ericwooshem/DIY-Frugal-Arduino-CO2-Sensor/Graphics/CO2_Sensor_Complete.png

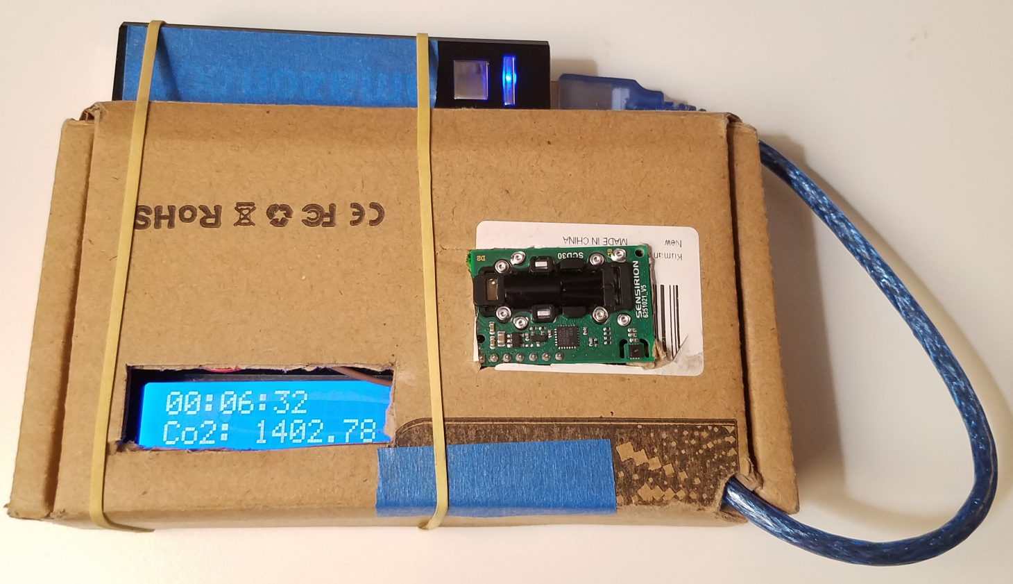
Graphics/CO2_Sensor_Complete.png
