ericwooshem/DIY-Frugal-Arduino-CO2-Sensor/Graphics/CO2_Sensor_Insides.png

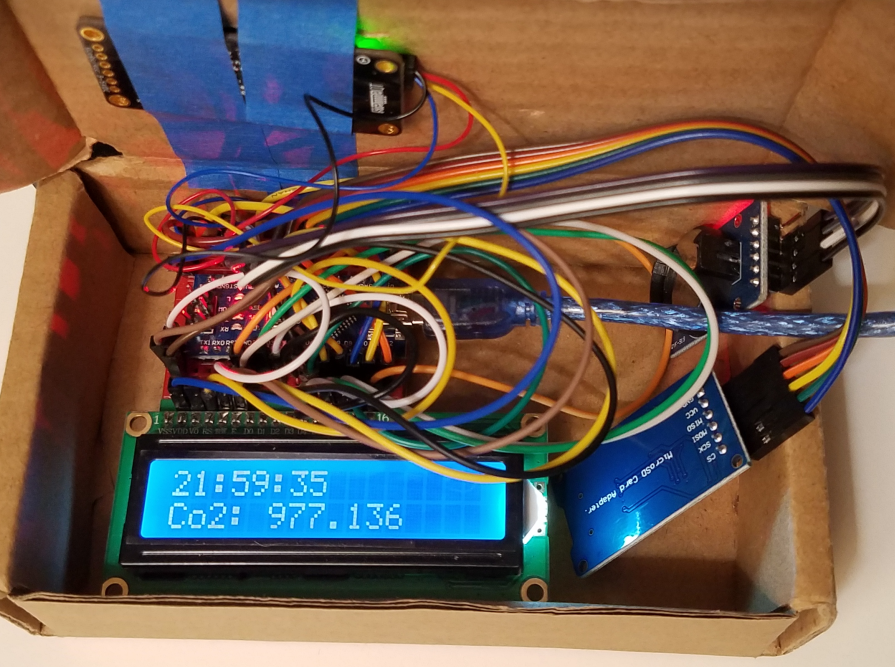
Graphics/CO2_Sensor_Insides.png
