ericwooshem/DIY-Frugal-Arduino-CO2-Sensor/Graphics/FileImporting/CO2_Excel_TextImportMethod.png

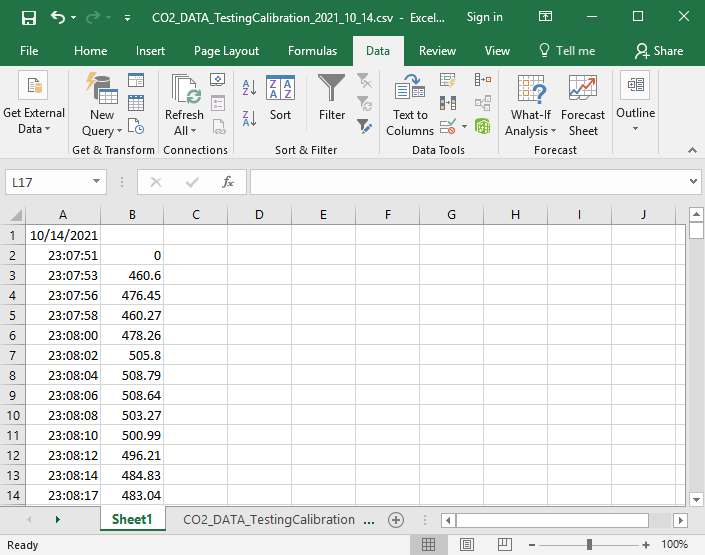
Graphics/FileImporting/CO2_Excel_TextImportMethod.png
