ericwooshem/DIY-Frugal-Arduino-CO2-Sensor/Graphics/FileImporting/CO2_Excel_UhOh.png

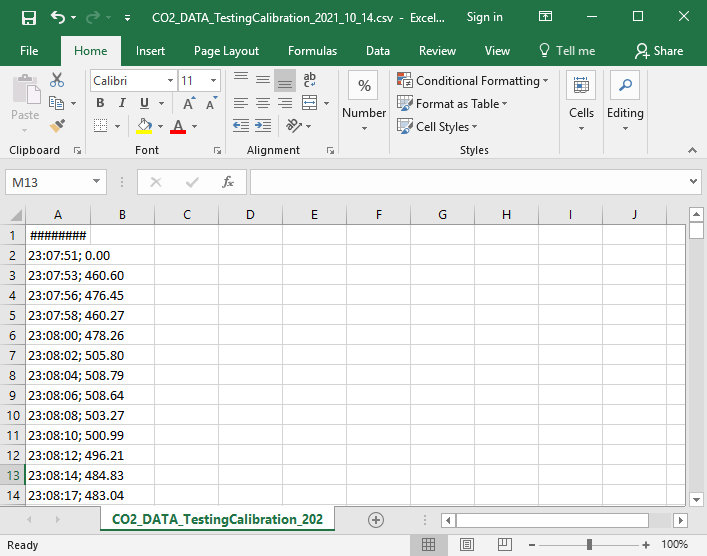
Graphics/FileImporting/CO2_Excel_UhOh.png
