ericwooshem/DIY-Frugal-Arduino-CO2-Sensor/Graphics/I12.png

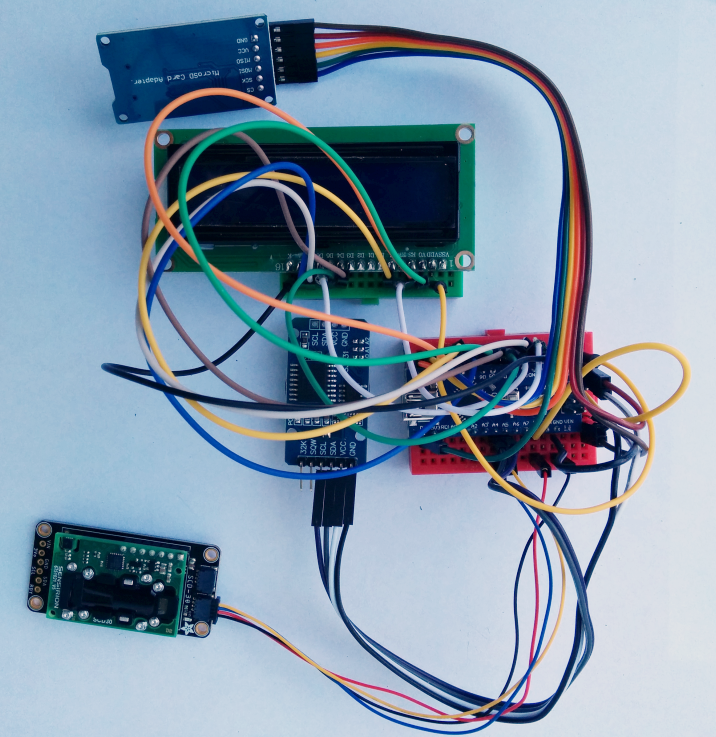
Graphics/I12.png
