ericwooshem/DIY-Frugal-Arduino-CO2-Sensor/Graphics/I13.png

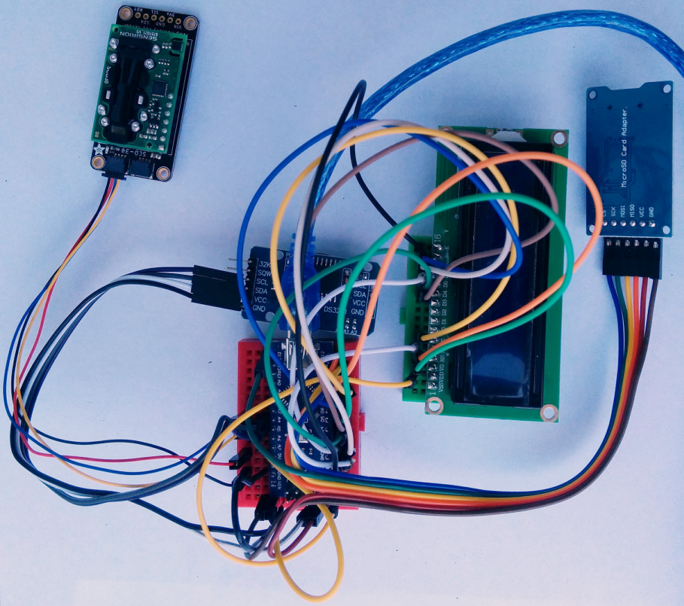
Graphics/I13.png
