ericwooshem/DIY-Frugal-Arduino-CO2-Sensor/Graphics/I14.png

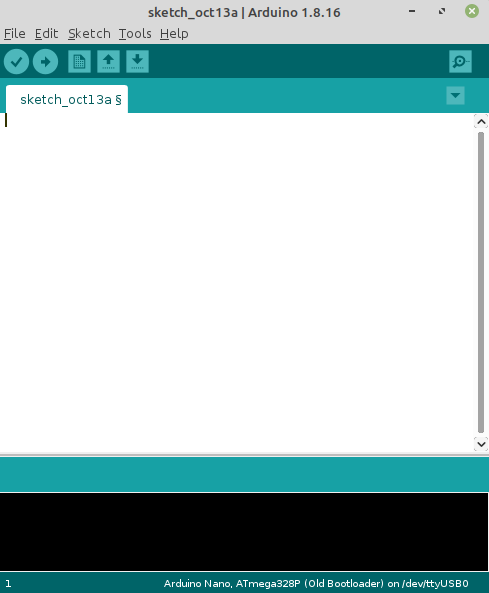
Graphics/I14.png
