ericwooshem/DIY-Frugal-Arduino-CO2-Sensor/Graphics/I17.png

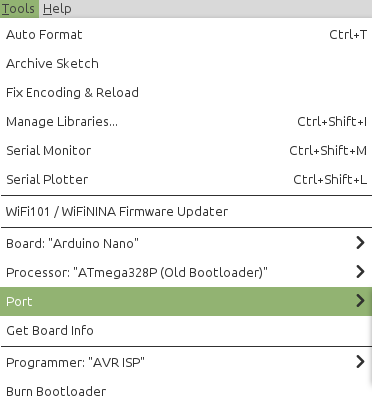
Graphics/I17.png
