ericwooshem/DIY-Frugal-Arduino-CO2-Sensor/Graphics/I19.png

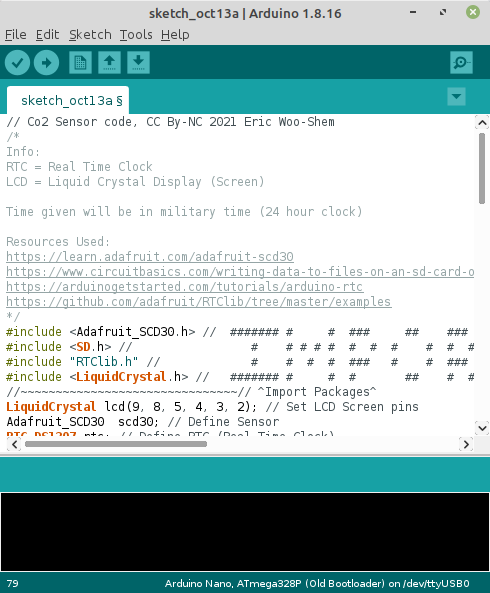
Graphics/I19.png
