ericwooshem/DIY-Frugal-Arduino-CO2-Sensor/Graphics/I20.png

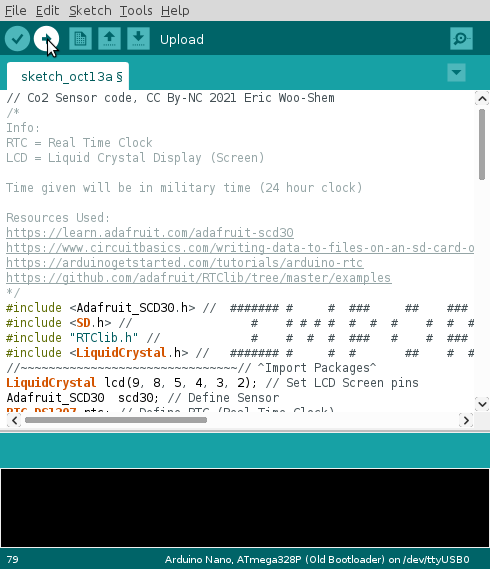
Graphics/I20.png
