ericwooshem/DIY-Frugal-Arduino-CO2-Sensor/Graphics/I21.png

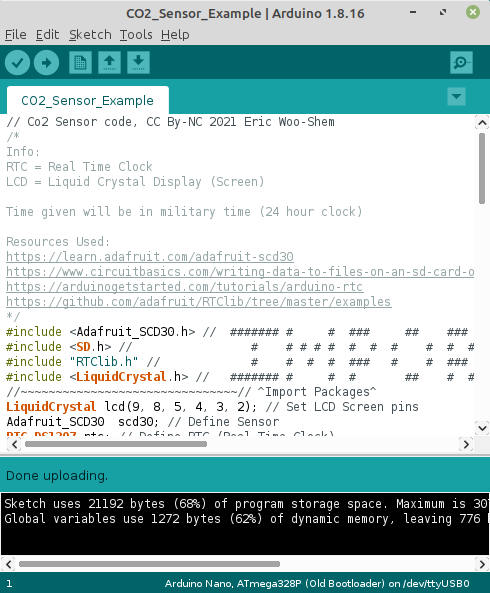
Graphics/I21.png
